jherkenhoff/STM/Mechanics/Vibration-Isolation/Plate_15.FCStd

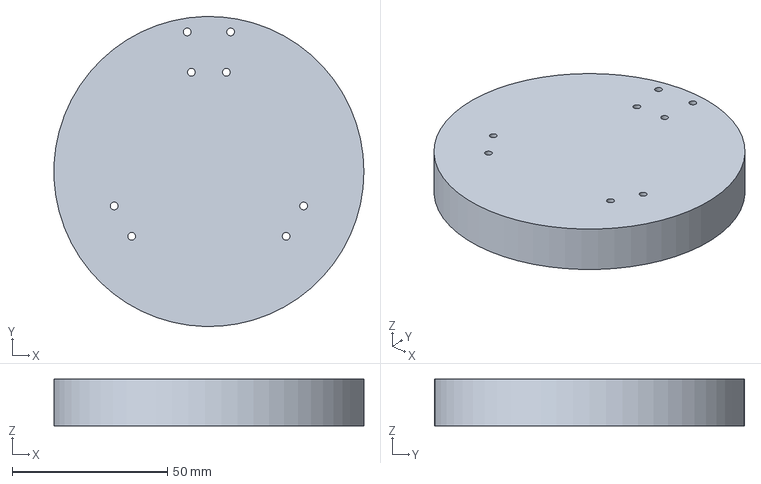
[picture p30: CAD file, 2019-08-25]
Mechanics/Vibration-Isolation/Plate_15.FCStd
99.9 x 100.0 x 15.0 mm
