jherkenhoff/STM/Electronics/Head-Interconnect/sma.stp

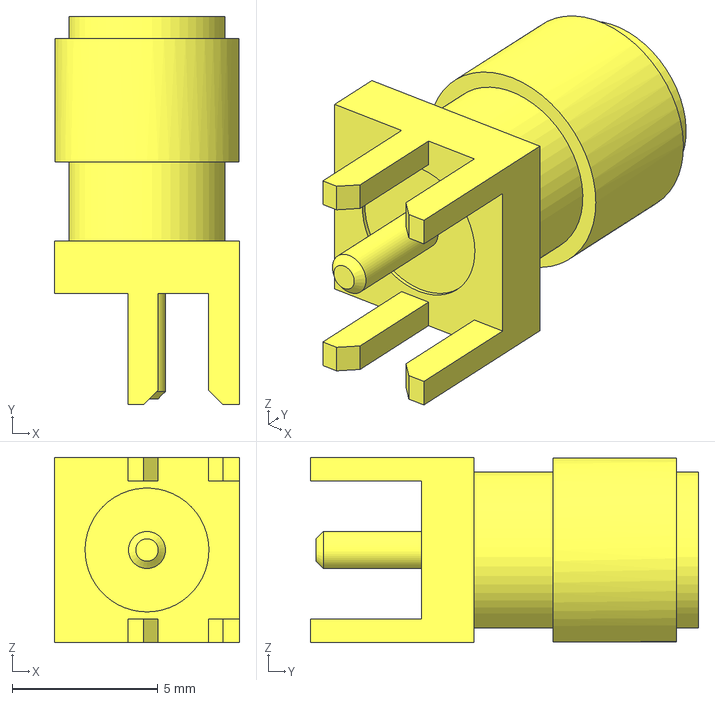
[picture p31: CAD file, 2019-08-25]
Electronics/Head-Interconnect/sma.stp
6.35 x 13.3 x 6.35 mm
