jherkenhoff/STM/Mechanics/Scanning-Head/Piezo-Press-Plate.FCStd

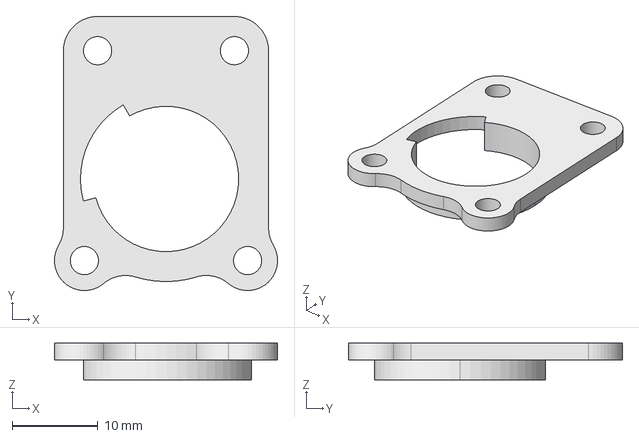
[picture p32: CAD file, 2021-05-17]
Mechanics/Scanning-Head/Piezo-Press-Plate.FCStd
26.1 x 32.0 x 4.30 mm
