jherkenhoff/STM/Mechanics/Vibration-Isolation/Plate_12.FCStd

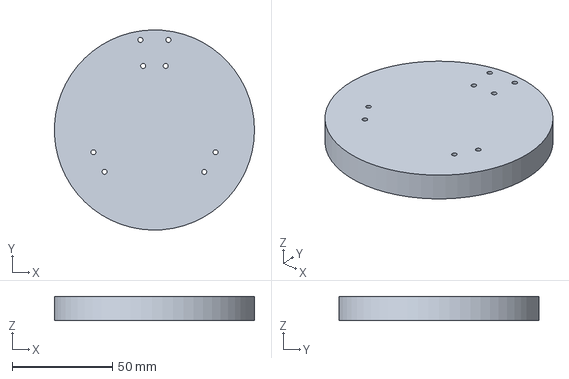
[picture p33: CAD file, 2019-08-25]
Mechanics/Vibration-Isolation/Plate_12.FCStd
99.9 x 100.0 x 12.0 mm
