jherkenhoff/STM/Mechanics/Scanning-Head/Tip-Holder.FCStd

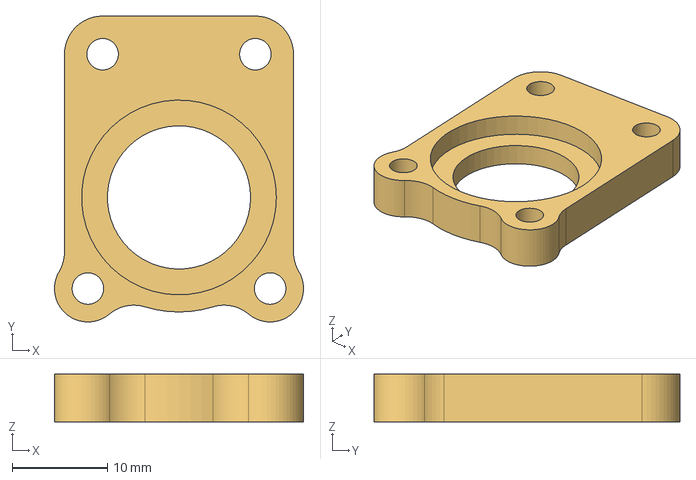
[picture p34: CAD file, 2021-05-17]
Mechanics/Scanning-Head/Tip-Holder.FCStd
26.1 x 32.0 x 5.00 mm
