jherkenhoff/STM/Mechanics/Vibration-Isolation/Viton-Fixture.FCStd

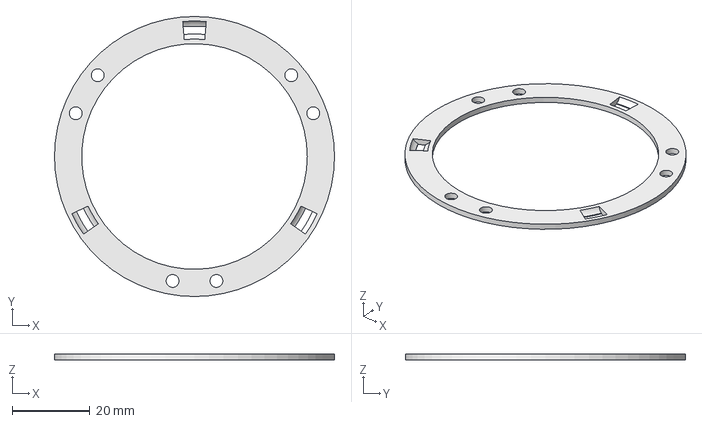
[picture p35: CAD file, 2019-08-25]
Mechanics/Vibration-Isolation/Viton-Fixture.FCStd
72.0 x 72.0 x 1.50 mm
