jherkenhoff/STM/Mechanics/Scanning-Head/Lower-Plate.FCStd

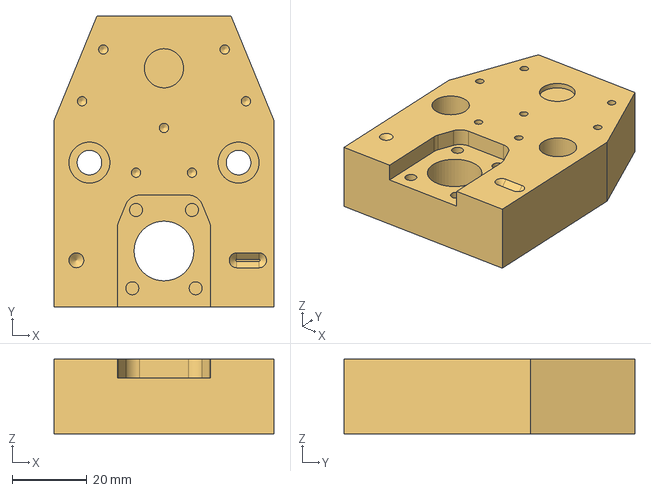
[picture p36: CAD file, 2020-10-09]
Mechanics/Scanning-Head/Lower-Plate.FCStd
59.0 x 78.0 x 20.0 mm
