jherkenhoff/STM/Mechanics/Vibration-Isolation/Plate_8.FCStd

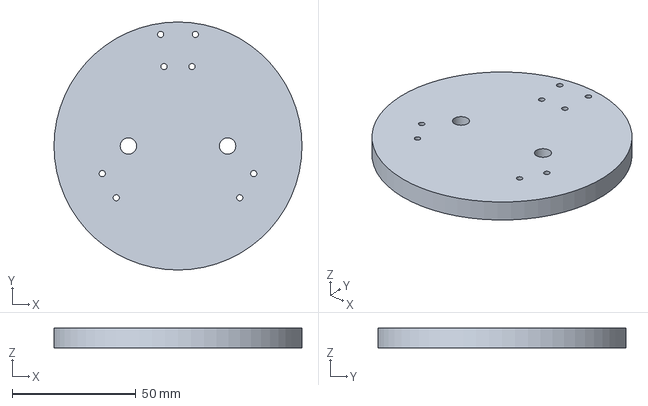
[picture p37: CAD file, 2019-08-25]
Mechanics/Vibration-Isolation/Plate_8.FCStd
100.0 x 100.0 x 8.00 mm
