jherkenhoff/STM/Mechanics/Scanning-Head/Lower-Plate-PCB-Outline.dxf

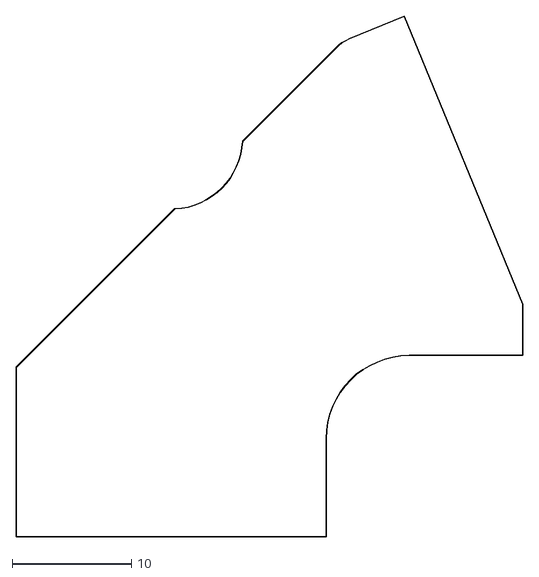
[picture p38: CAD file, 2020-10-09]
Mechanics/Scanning-Head/Lower-Plate-PCB-Outline.dxf
42.5 x 43.7
