jherkenhoff/STM/Mechanics/Vibration-Isolation/Viton.FCStd

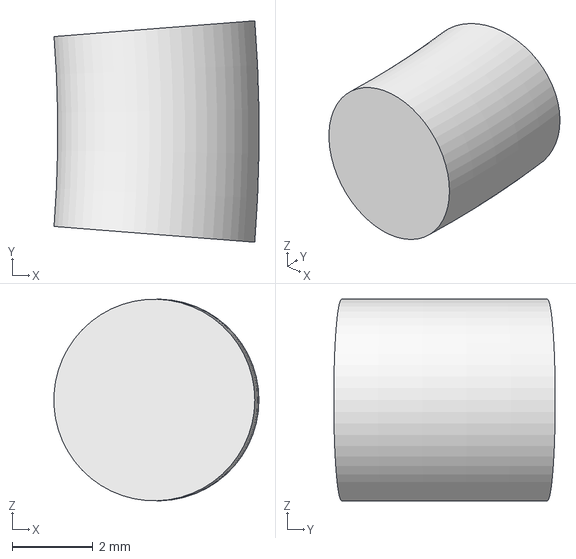
[picture p39: CAD file, 2019-08-25]
Mechanics/Vibration-Isolation/Viton.FCStd
5.08 x 5.49 x 5.00 mm
