jherkenhoff/STM/Mechanics/Scanning-Head/Upper-Plate.FCStd

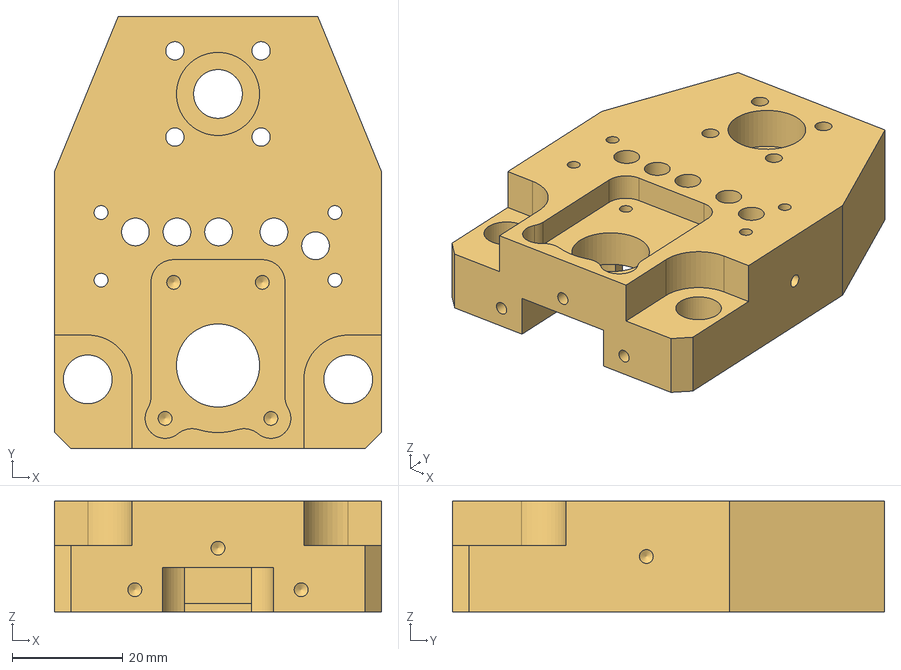
[picture p40: CAD file, 2020-07-15]
Mechanics/Scanning-Head/Upper-Plate.FCStd
59.0 x 78.0 x 20.0 mm
