jherkenhoff/STM/Mechanics/Scanning-Head/Probe-Holder.FCStd

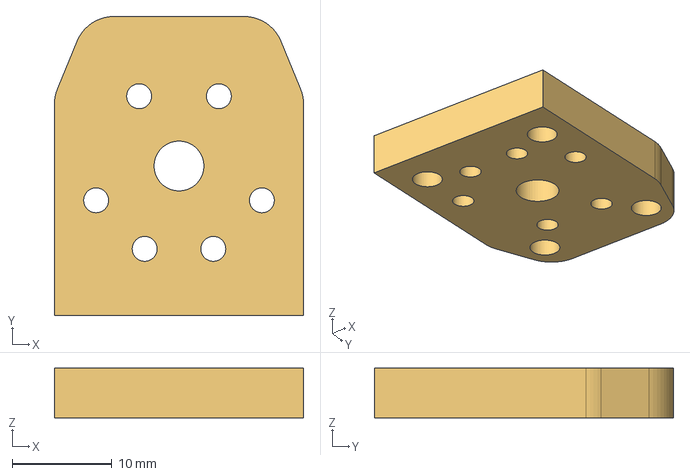
[picture p41: CAD file, 2019-08-25]
Mechanics/Scanning-Head/Probe-Holder.FCStd
25.0 x 30.0 x 5.00 mm
