jherkenhoff/STM/Mechanics/Scanning-Head/Amp-Plate.FCStd

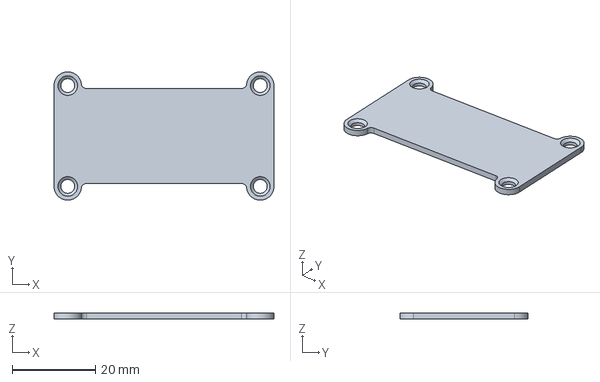
[picture p42: CAD file, 2019-08-25]
Mechanics/Scanning-Head/Amp-Plate.FCStd
52.8 x 30.8 x 1.50 mm
