jherkenhoff/STM/Mechanics/Scanning-Head/Piezo.FCStd

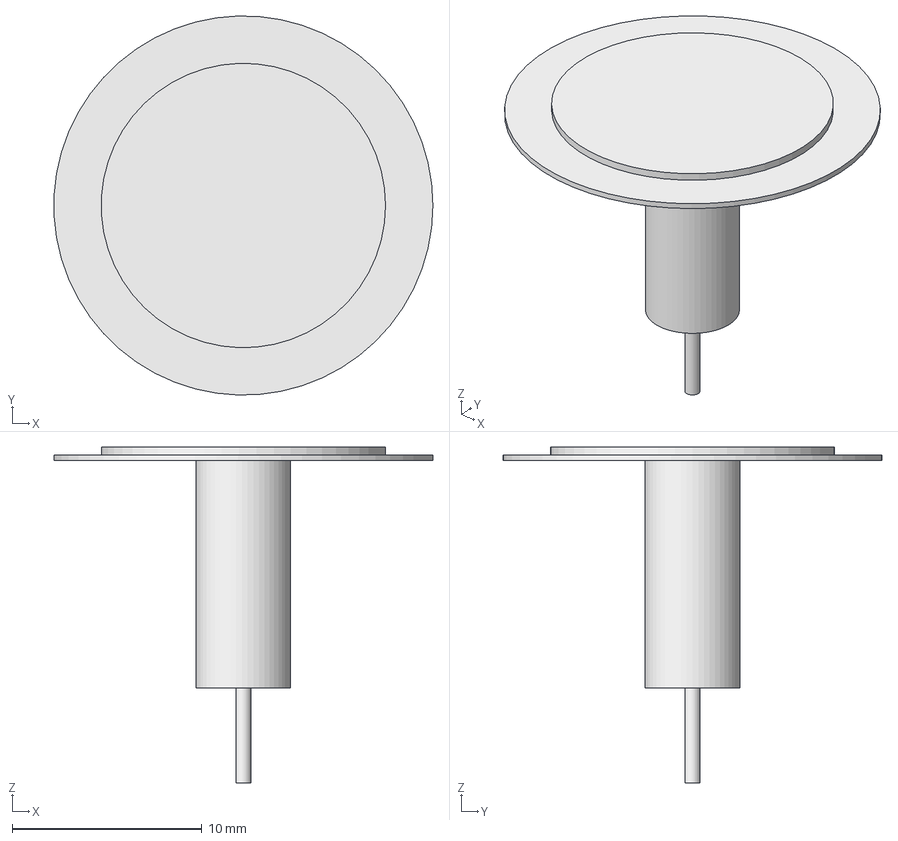
[picture p43: CAD file, 2019-08-25]
Mechanics/Scanning-Head/Piezo.FCStd
20.0 x 20.0 x 17.7 mm
